HarrySkySon/BitForge-SDR/schematics/All_Bloks_of_project.kicad_sch

## KiCad design schematics/All_Bloks_of_project.kicad_sch (2026-03-29)

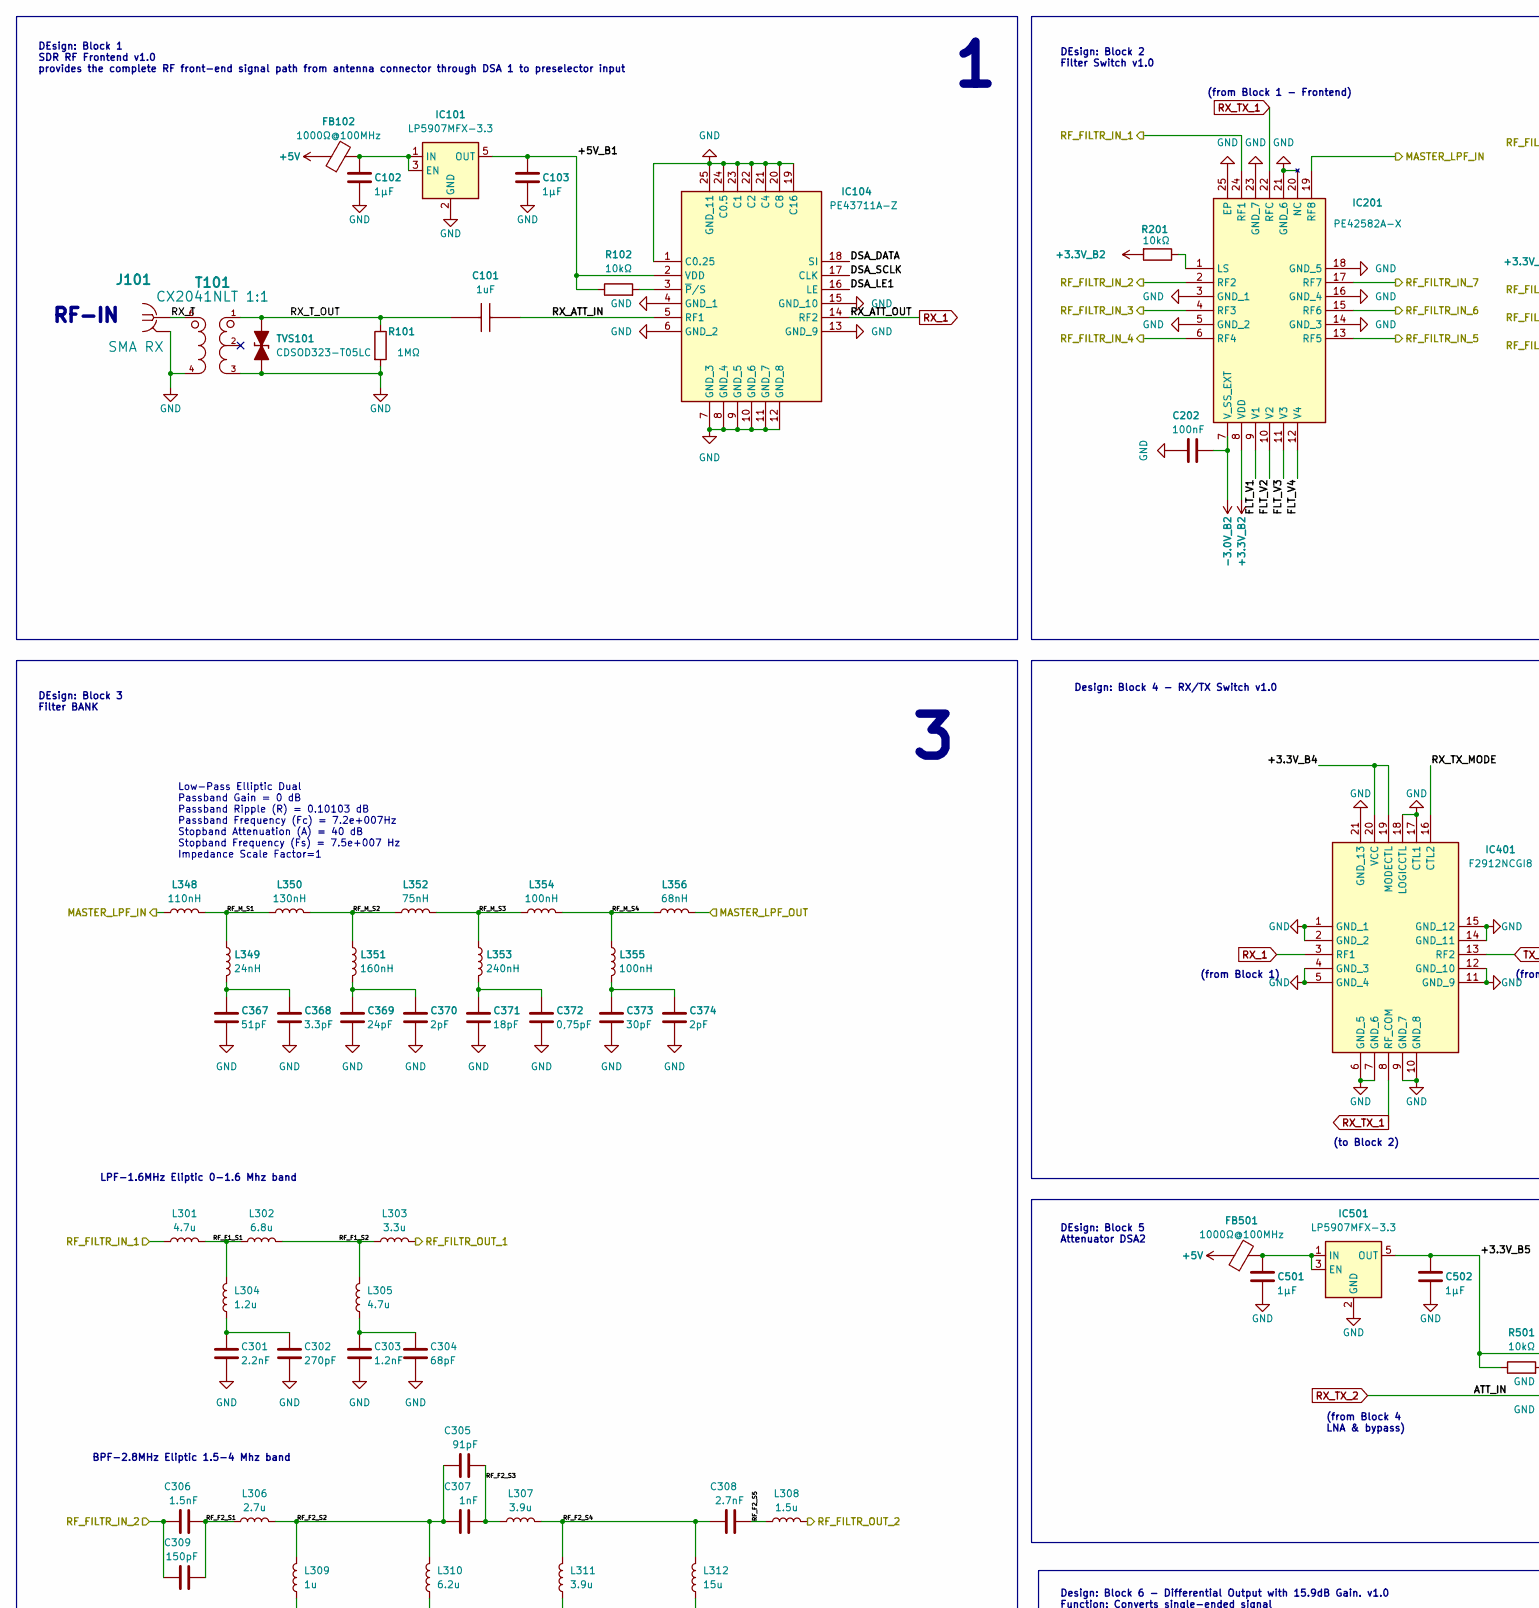
[picture p2: schematic All_Bloks_of_project.kicad_sch, part in row 1, column 1]

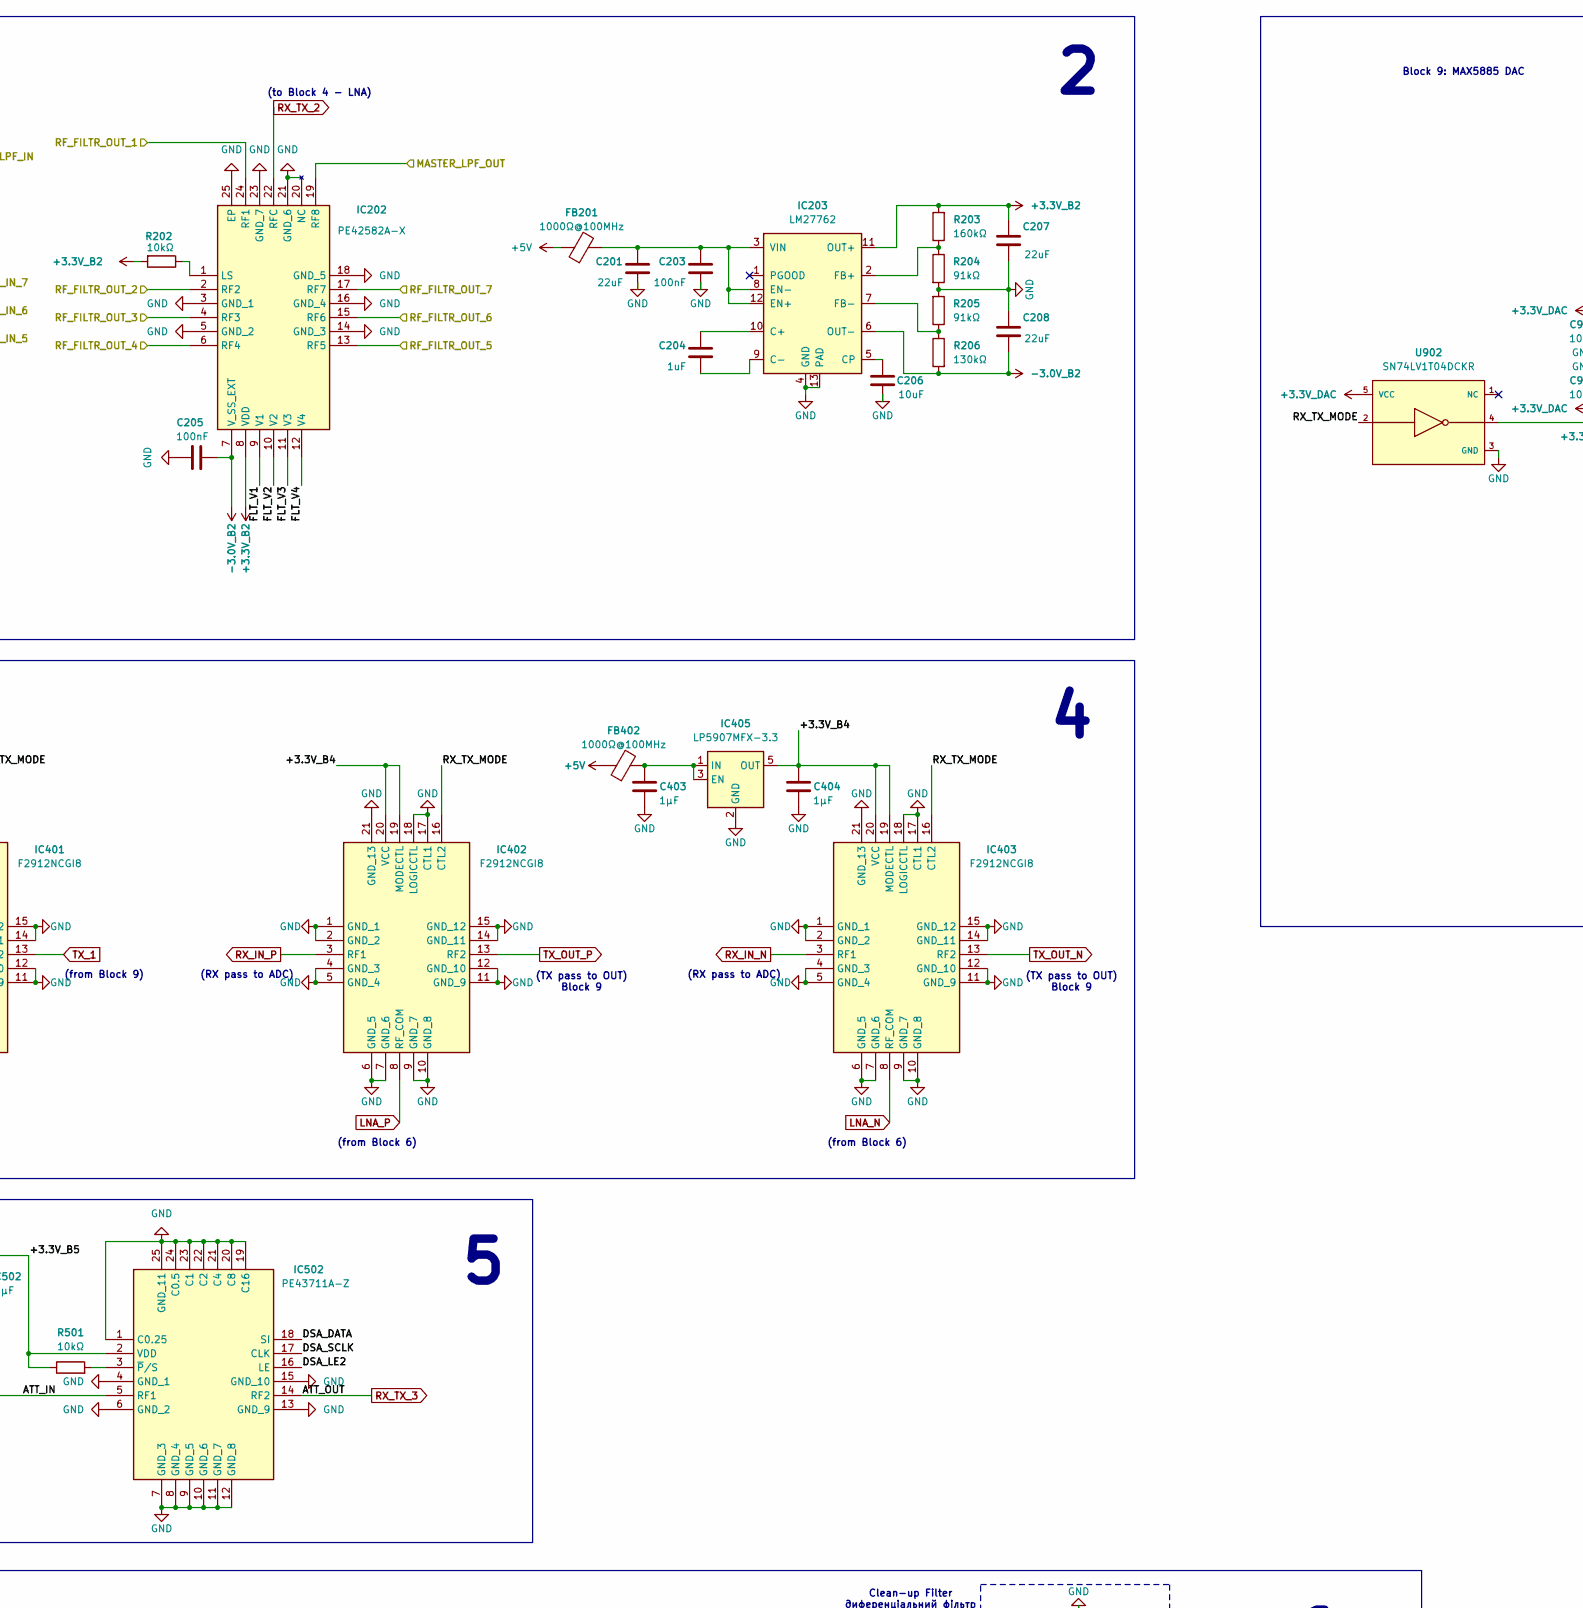
[picture p3: schematic All_Bloks_of_project.kicad_sch, part in row 1, column 2]

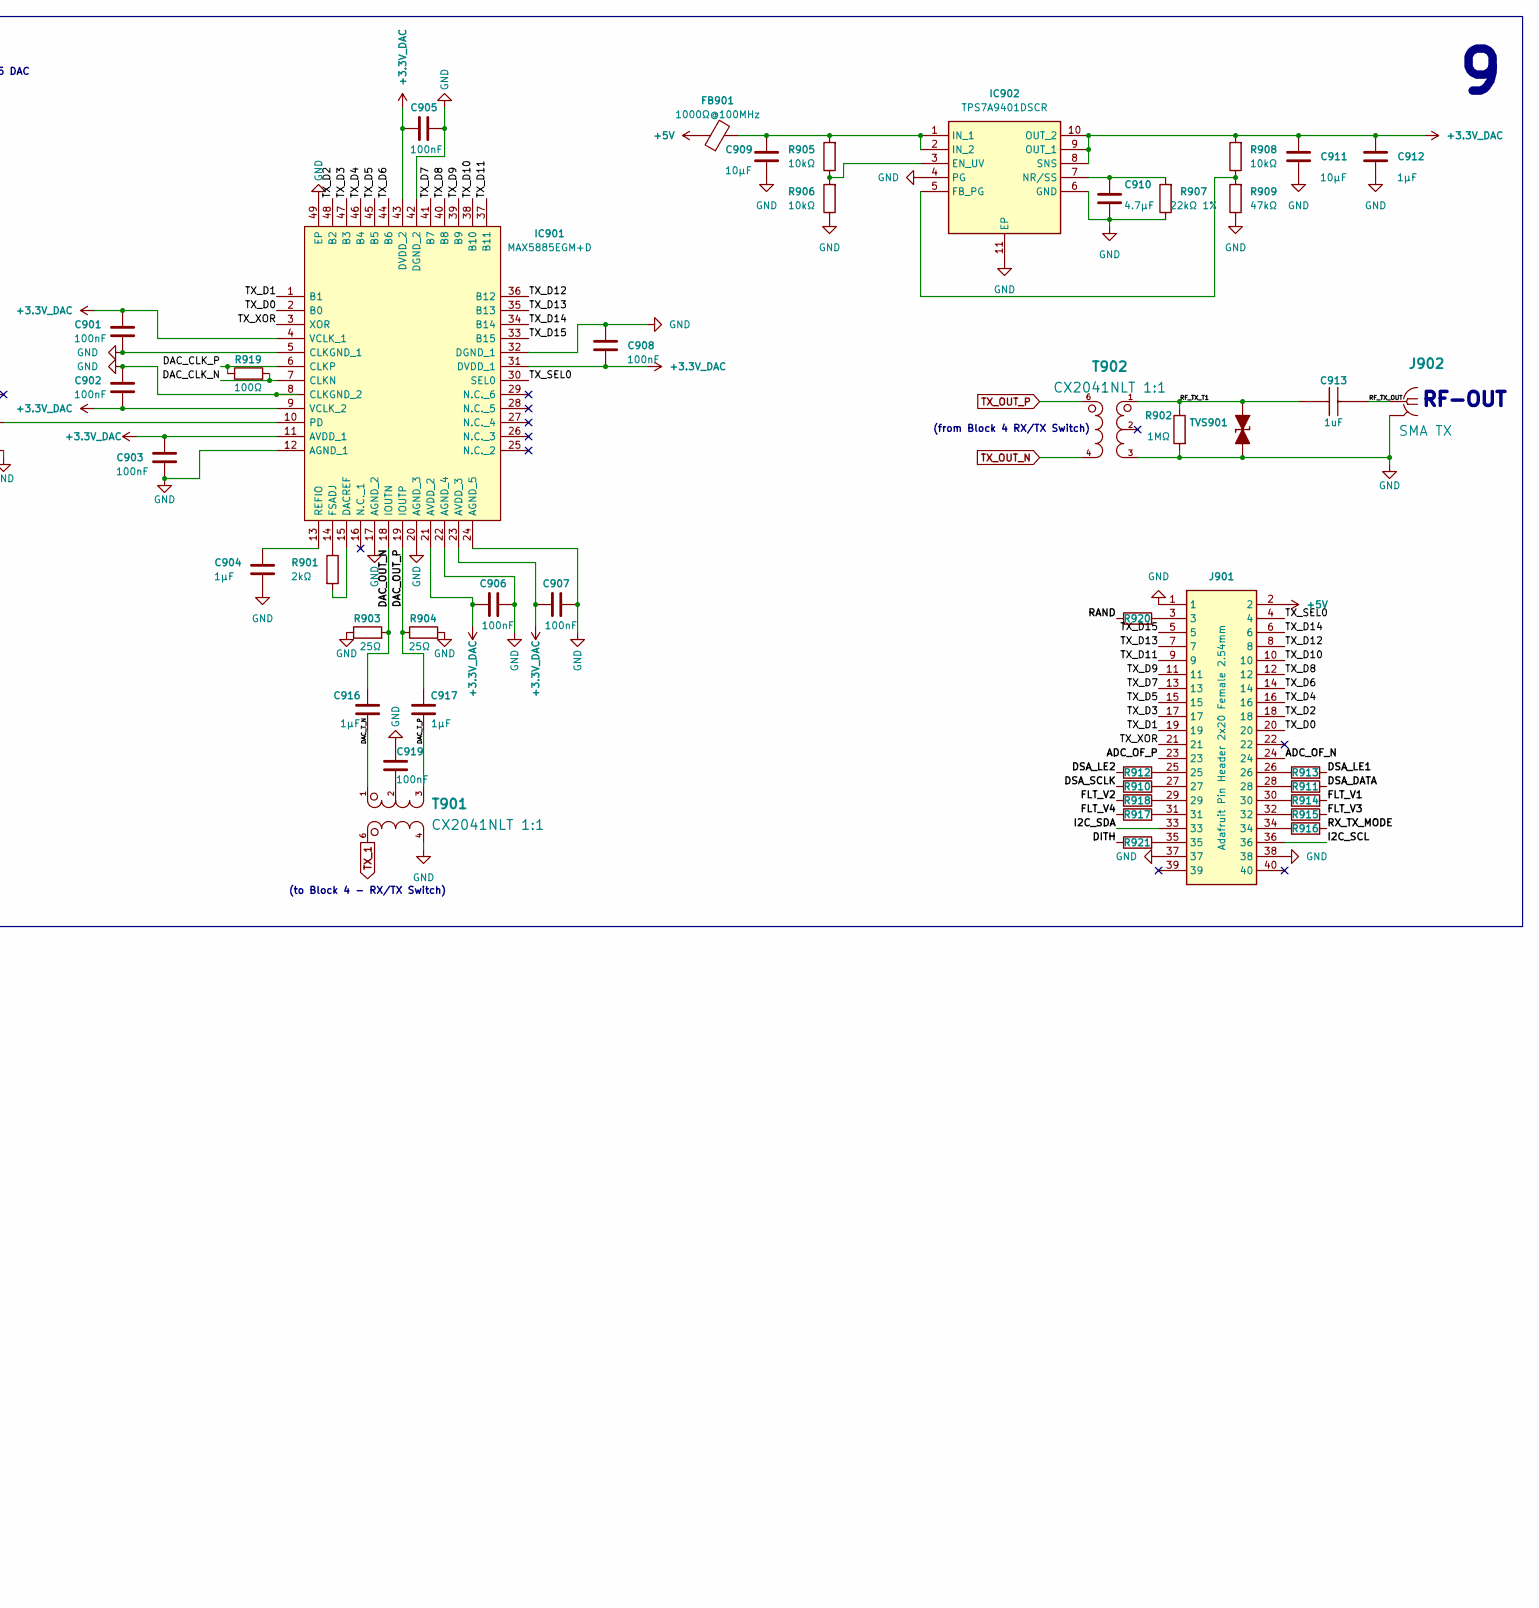
[picture p4: schematic All_Bloks_of_project.kicad_sch, part in row 1, column 3]

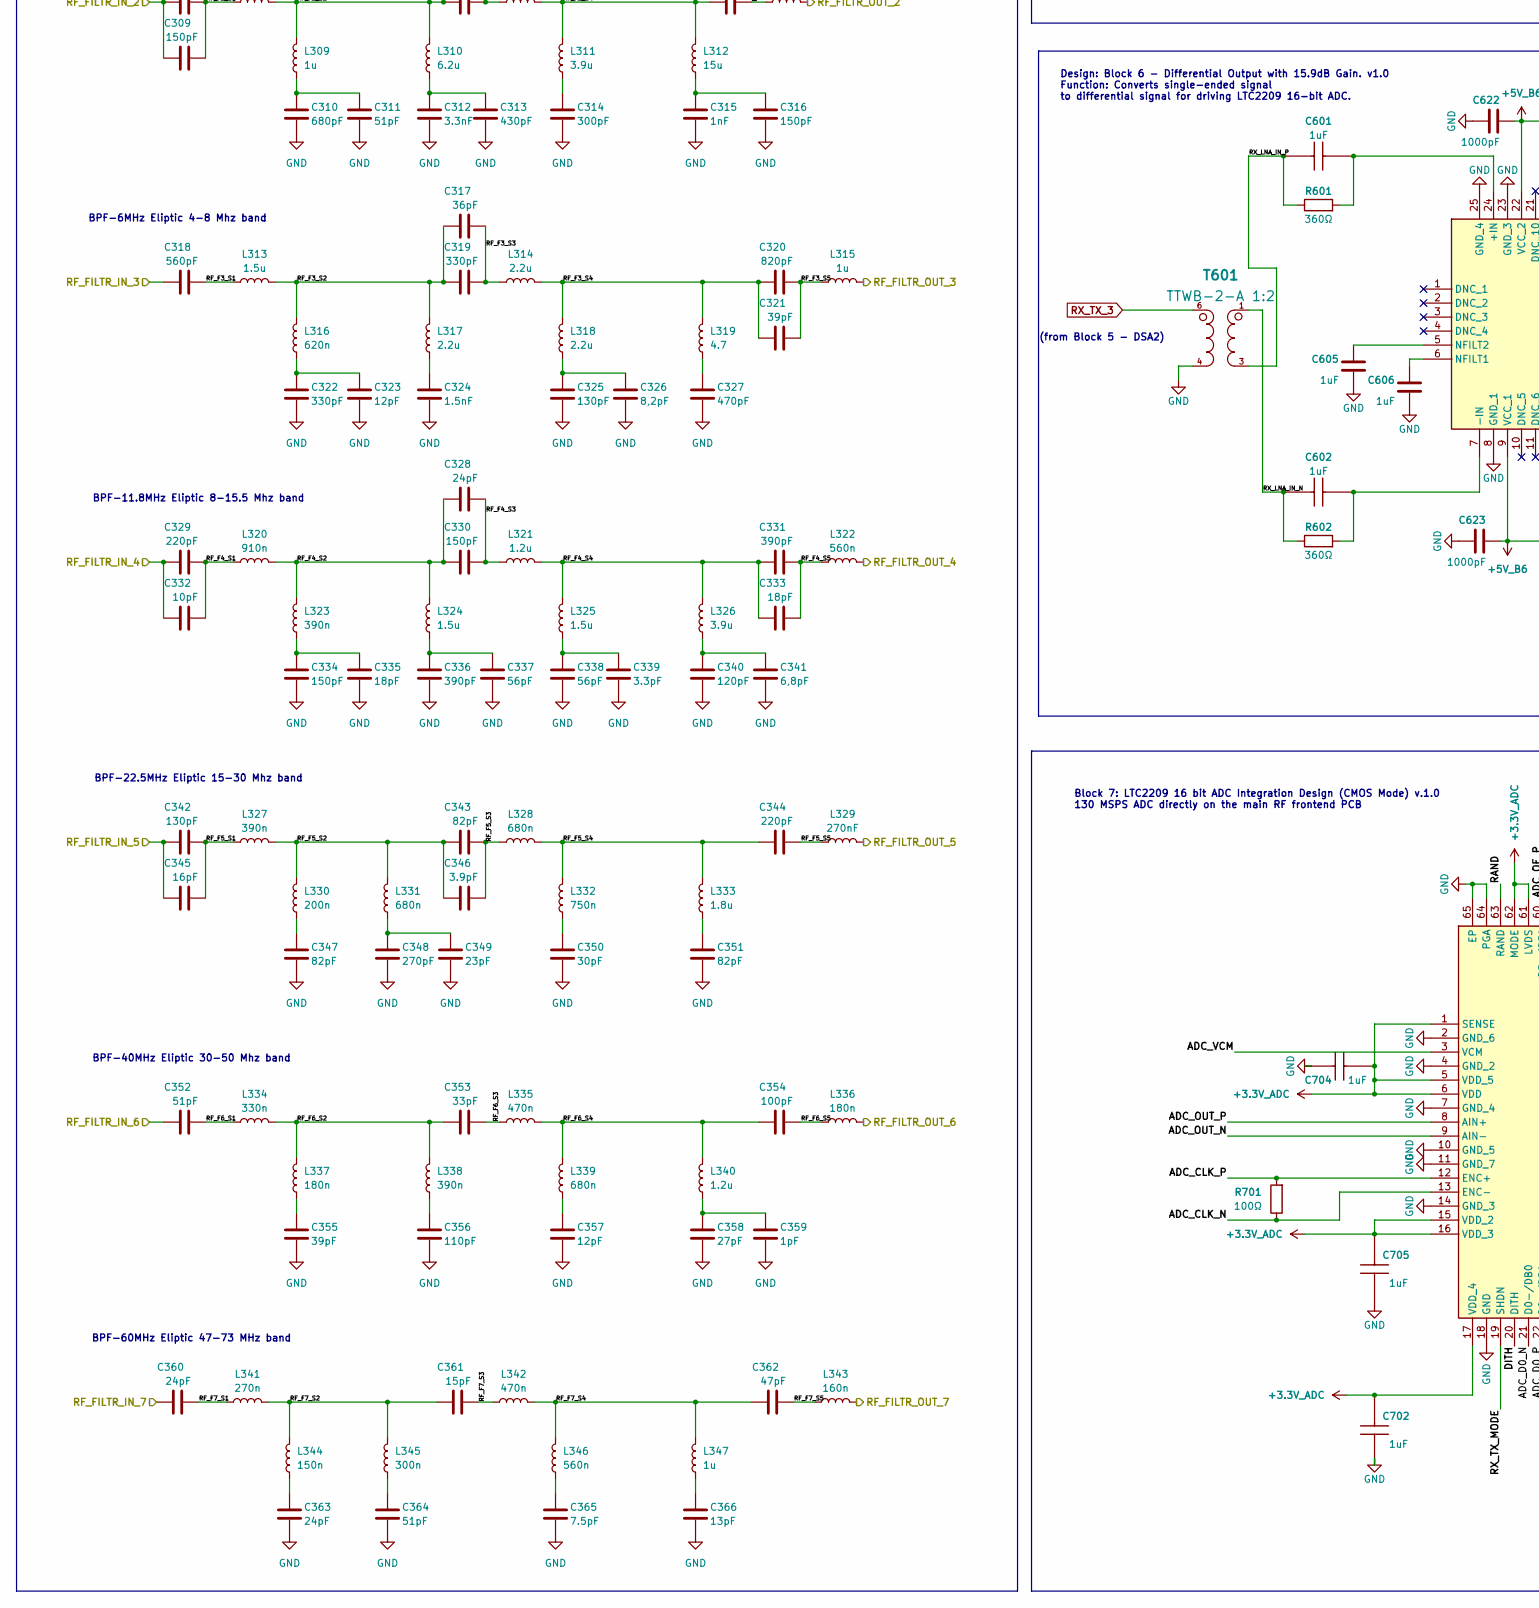
[picture p5: schematic All_Bloks_of_project.kicad_sch, part in row 2, column 1]

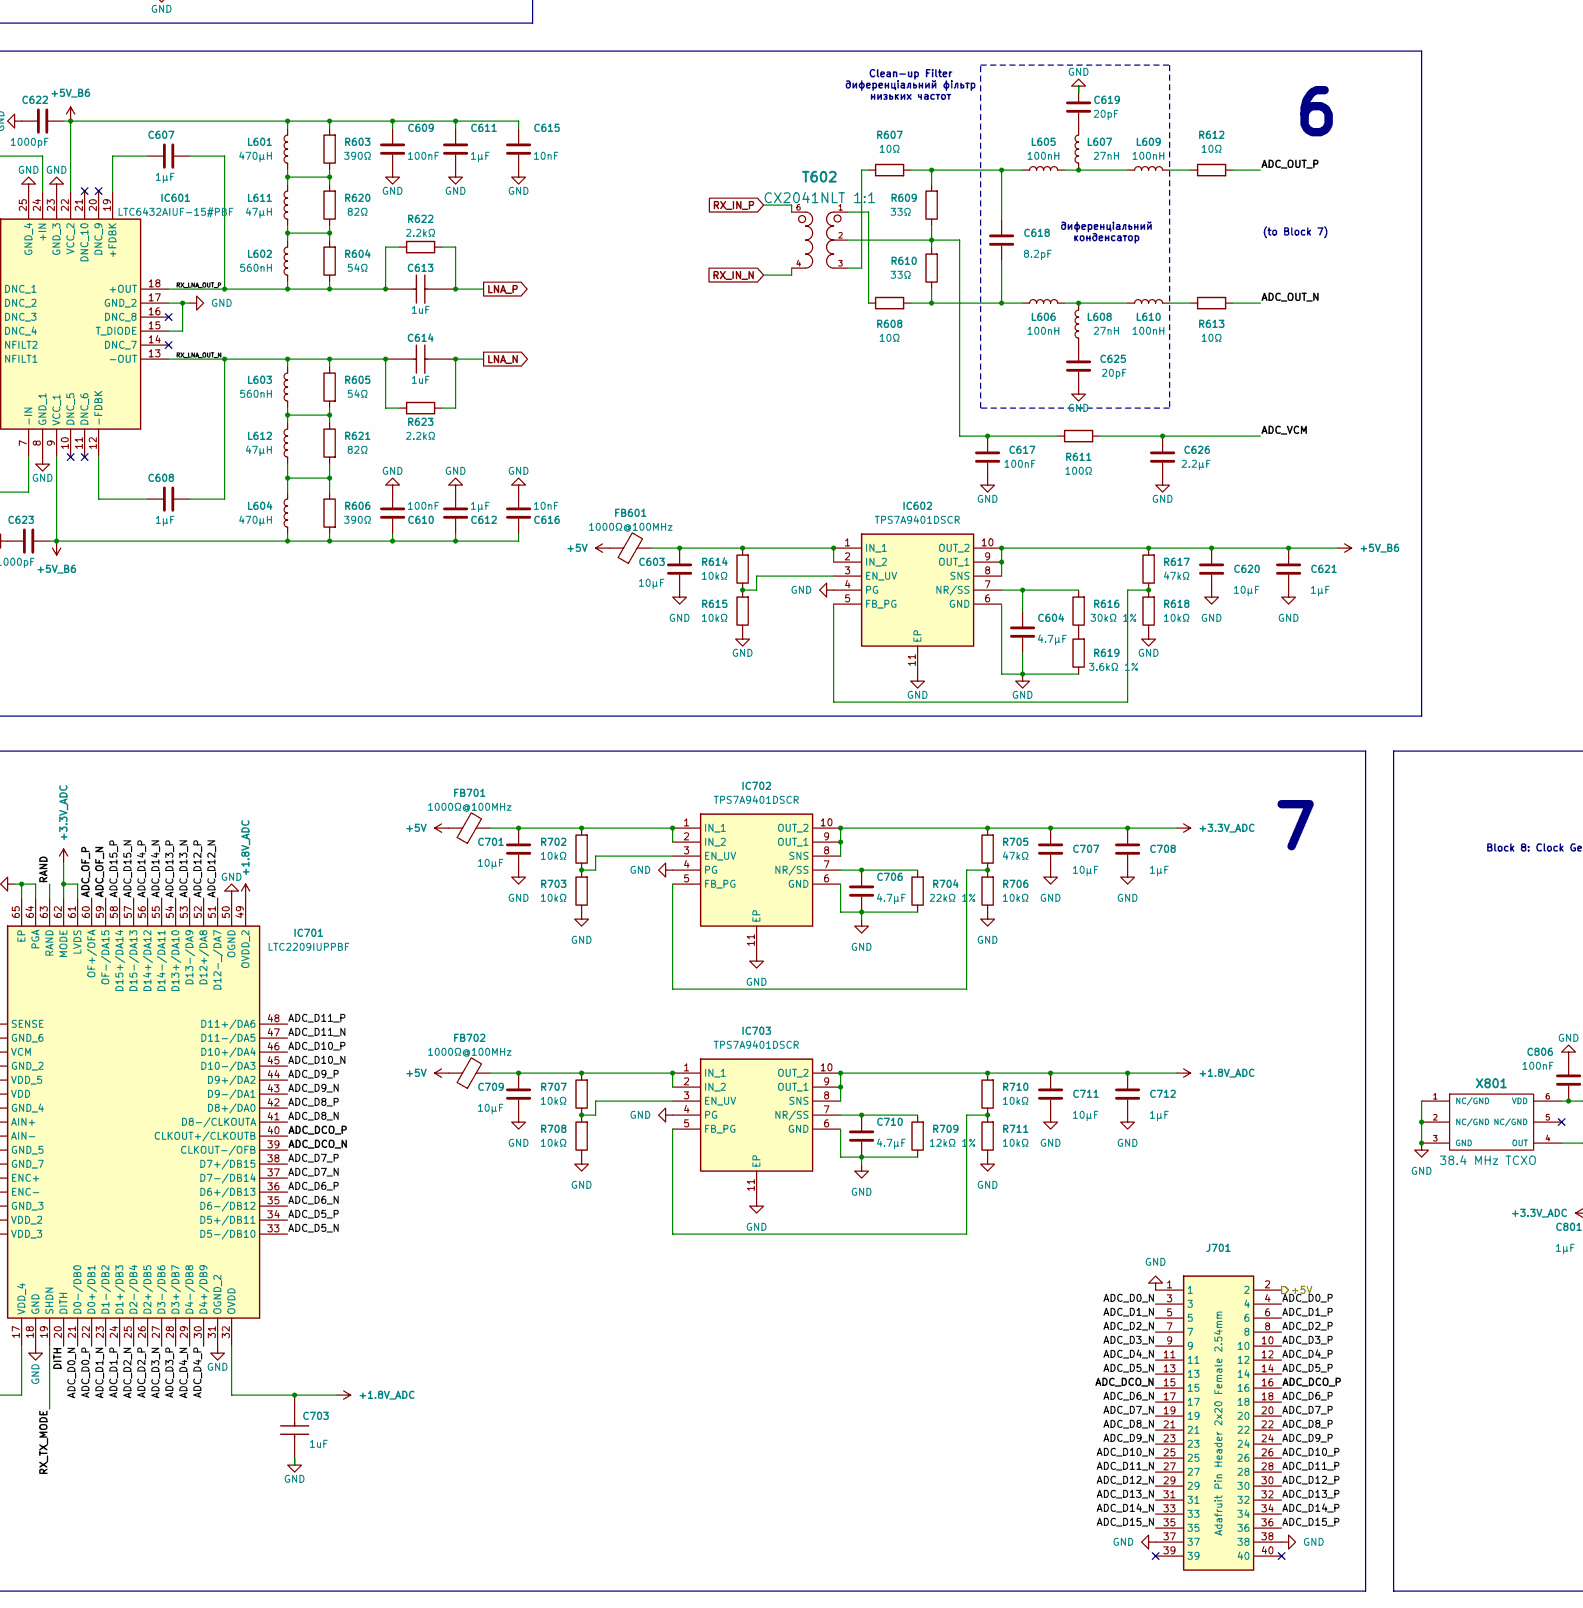
[picture p6: schematic All_Bloks_of_project.kicad_sch, part in row 2, column 2]

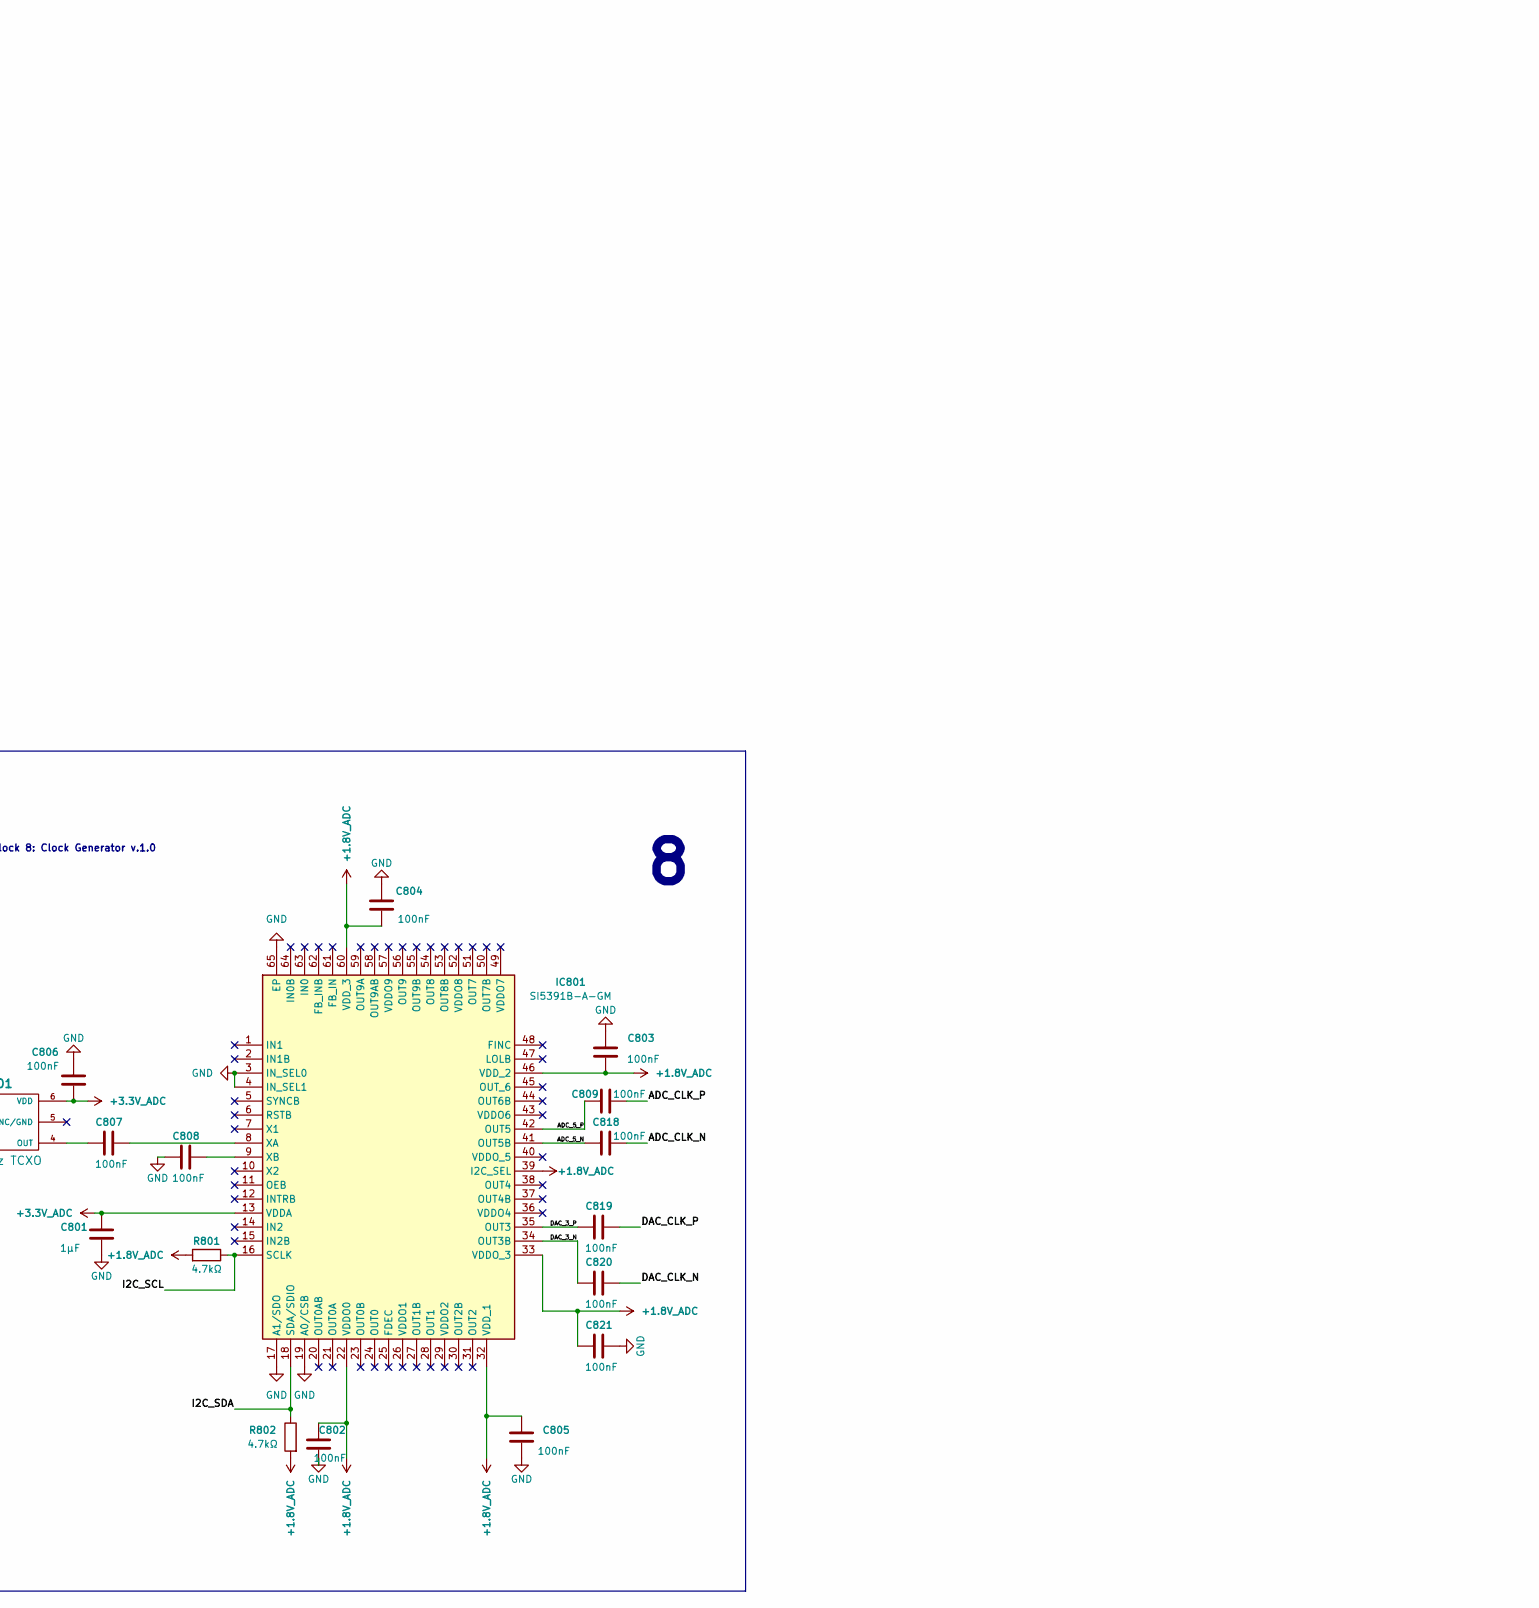
[picture p7: schematic All_Bloks_of_project.kicad_sch, part in row 2, column 3]

Parts:
C101, C601, C602, C613, C614, C702, C703, C704, C705, C913: 1uF; 0508; Manufacturer_Part_Number 0508ZC105KAT2A; Mouser Part Number 581-0508ZC105K
C102, C103, C403, C404, C501, C502, C607, C608, C621, C708, C712, C801, C904, C912: 1µF; C_0603_1608Metric
C201, C207, C208: 22uF; C_0603_1608Metric
C202, C203, C205, C617, C802, C803, C804, C805, C806, C807, C808, C809, C818, C819, C820, C821, C901, C902, C903, C905, C906, C907, C908, C919: 100nF; C_0603_1608Metric
C204, C605, C606: 1uF; C_0603_1608Metric
C206: 10uF; C_0603_1608Metric
C301: 2.2nF; C_0603_1608Metric
C302, C348: 270pF; C_0603_1608Metric
C303: 1.2nF; C_0603_1608Metric
C304: 68pF; C_0603_1608Metric
C305: 91pF; C_0603_1608Metric
C306, C324: 1.5nF; C_0603_1608Metric
C307, C315: 1nF; C_0603_1608Metric
C308: 2.7nF; C_0603_1608Metric
C309, C316, C330, C334: 150pF; C_0603_1608Metric
C310: 680pF; C_0603_1608Metric
C311, C352, C364, C367: 51pF; C_0603_1608Metric
C312: 3.3nF; C_0603_1608Metric
C313: 430pF; C_0603_1608Metric
C314: 300pF; C_0603_1608Metric
C317: 36pF; C_0603_1608Metric
C318: 560pF; C_0603_1608Metric
C319, C322: 330pF; C_0603_1608Metric
C320: 820pF; C_0603_1608Metric
C321, C355: 39pF; C_0603_1608Metric
C323, C357: 12pF; C_0603_1608Metric
C325, C342: 130pF; C_0603_1608Metric
C326: 8,2pF; C_0603_1608Metric
C327: 470pF; C_0603_1608Metric
C328, C360, C363, C369: 24pF; C_0603_1608Metric
C329, C344: 220pF; C_0603_1608Metric
C331, C336: 390pF; C_0603_1608Metric
C332: 10pF; C_0603_1608Metric
C333, C335, C371: 18pF; C_0603_1608Metric
C337, C338: 56pF; C_0603_1608Metric
C339, C368: 3.3pF; C_0603_1608Metric
C340: 120pF; C_0603_1608Metric
C341: 6,8pF; C_0603_1608Metric
C343, C347, C351: 82pF; C_0603_1608Metric
C345: 16pF; C_0603_1608Metric
C346: 3.9pF; C_0603_1608Metric
C349: 23pF; C_0603_1608Metric
C350, C373: 30pF; C_0603_1608Metric
C353: 33pF; C_0603_1608Metric
C354: 100pF; C_0603_1608Metric
C356: 110pF; C_0603_1608Metric
C358: 27pF; C_0603_1608Metric
C359: 1pF; C_0603_1608Metric
C361: 15pF; C_0603_1608Metric
C362: 47pF; C_0603_1608Metric
C365: 7.5pF; C_0603_1608Metric
C366: 13pF; C_0603_1608Metric
C370, C374: 2pF; C_0603_1608Metric
C372: 0,75pF; C_0603_1608Metric
C603, C620, C701, C707, C709, C711, C909, C911: 10µF; C_0603_1608Metric
C604, C706, C710, C910: 4.7µF; C_0603_1608Metric
C609, C610: 100nF; L_0805_2012Metric
C611, C612: 1µF; L_0805_2012Metric
C615, C616: 10nF; L_0805_2012Metric
C618: 8.2pF; C_0603_1608Metric
C619, C625: 20pF; C_0603_1608Metric
C622, C623: 1000pF; C_0603_1608Metric
C626: 2.2µF; C_0603_1608Metric
C916, C917: 1µF; C_0805_2012Metric
FB102, FB201, FB402, FB501, FB601, FB701, FB702, FB901: 1000Ω@100MHz; L_0603_1608Metric
IC101, IC405, IC501: LP5907MFX-3.3; SOT-23-5
IC104, IC502: PE43711A-Z; QFN50P400X400X90-25N-D; Manufacturer_Part_Number PE43711A-Z
IC201, IC202: PE42582A-X; QFN50P400X400X90-25N-D; Manufacturer_Part_Number PE42582A-X; Mouser Part Number 81-PE42582A-X
IC203: LM27762; WSON-12-1EP_3x2mm_P0.5mm_EP1x2.65_ThermalVias
IC401, IC402, IC403: F2912NCGI8; QFN50P400X400X80-21N-D; Mouser Part Number 972-F2912NCGI8
IC601: LTC6432AIUF-15#PBF; QFN50P400X400X80-25N-D; Mouser Part Number 584-6432AIUF15PBF
IC602, IC702, IC703, IC902: TPS7A9401DSCR; SON50P300X300X80-11N-D; Manufacturer_Part_Number TPS7A9401DSCR; Mouser Part Number 595-TPS7A9401DSCR
IC701: LTC2209IUPPBF; QFN50P900X900X80-65N; Manufacturer_Part_Number LTC2209IUPPBF
IC801: SI5391B-A-GM; QFN50P900X900X90-65N-D; Manufacturer_Part_Number SI5391B-A-GM; Mouser Part Number 634-SI5391B-A-GM
IC901: MAX5885EGM+D; QFN50P700X700X100-49N; Manufacturer_Part_Number MAX5885EGM+D; Mouser Part Number 700-MAX5885EGMD
J101: SMA RX; SMA_BAT_Wireless_BWSMA-KWE-Z001
J701, J901: Adafruit Pin Header 2x20 Female 2.54mm; PinHeader_2x20_P2.54mm_Vertical; Manufacturer_Part_Number 2222; Mouser Part Number 485-2222
J902: SMA TX; SMA_BAT_Wireless_BWSMA-KWE-Z001
L301, L305: 4.7u; L_1008_2520Metric
L302: 6.8u; L_1210_3225Metric
L303: 3.3u; L_1008_2520Metric
L304, L321, L340: 1.2u; L_1008_2520Metric
L306: 2.7u; L_1008_2520Metric
L307, L311, L326: 3.9u; L_1008_2520Metric
L308, L313, L324, L325: 1.5u; L_1008_2520Metric
L309, L315, L347: 1u; L_1008_2520Metric
L310: 6.2u; L_1008_2520Metric
L312: 15u; L_1008_2520Metric
L314, L317, L318: 2.2u; L_1008_2520Metric
L316: 620n; L_1008_2520Metric
L319: 4.7; L_1008_2520Metric
L320: 910n; L_1008_2520Metric
L322, L346: 560n; L_1008_2520Metric
L323, L327, L338: 390n; L_1008_2520Metric
L328, L331, L339: 680n; L_1008_2520Metric
L329: 270nF; L_1008_2520Metric
L330: 200n; L_0603_1608Metric
L332: 750n; L_1008_2520Metric
L333: 1.8u; L_1008_2520Metric
L334: 330n; L_1008_2520Metric
L335, L342: 470n; L_1008_2520Metric
L336, L337: 180n; L_0603_1608Metric
L341: 270n; L_1008_2520Metric
L343: 160n; L_0603_1608Metric
L344: 150n; L_1008_2520Metric
L345: 300n; L_0603_1608Metric
L348: 110nH; L_0603_1608Metric
L349: 24nH; L_0603_1608Metric
L350: 130nH; L_0603_1608Metric
L351: 160nH; L_0603_1608Metric
L352: 75nH; L_0603_1608Metric
L353: 240nH; L_0805_2012Metric
L354, L355, L605, L606, L609, L610: 100nH; L_0603_1608Metric
L356: 68nH; L_0603_1608Metric
L601, L604: 470µH; L_Changjiang_FNR8065S
L602, L603: 560nH; L_Sunlord_SWPA252010S
L607, L608: 27nH; L_0603_1608Metric
L611, L612: 47µH; L_Sunlord_SWPA4030S
R101, R902: 1MΩ; R_0603_1608Metric
R102, R201, R202, R501, R614, R615, R618, R702, R703, R706, R707, R708, R710, R711, R905, R906, R908: 10kΩ; R_0603_1608Metric
R203: 160kΩ; R_0603_1608Metric
R204, R205: 91kΩ; R_0603_1608Metric
R206: 130kΩ; R_0603_1608Metric
R601, R602: 360Ω; R_0603_1608Metric
R603, R606: 390Ω; R_0603_1608Metric
R604, R605: 54Ω; R_0603_1608Metric
R607, R608, R612, R613: 10Ω; R_0603_1608Metric
R609, R610: 33Ω; R_0603_1608Metric
R611, R701, R919: 100Ω; R_0603_1608Metric
R616: 30kΩ 1%; R_0603_1608Metric
R617, R705, R909: 47kΩ; R_0603_1608Metric
R619: 3.6kΩ 1%; R_0603_1608Metric
R620, R621: 82Ω; R_0603_1608Metric
R622, R623: 2.2kΩ; R_0603_1608Metric
R704, R907: 22kΩ 1%; R_0603_1608Metric
R709: 12kΩ 1%; R_0603_1608Metric
R801, R802: 4.7kΩ; R_0603_1608Metric
R901: 2kΩ; R_0603_1608Metric
R903, R904: 25Ω; R_0603_1608Metric
R910, R911, R912, R913, R914, R915, R916, R917, R918, R920, R921: 47Ω; R_0603_1608Metric
T101, T602, T901, T902: CX2041NLT 1:1; CX2041NLT
T601: TTWB-2-A 1:2; TTWB20101LB
TVS101, TVS901: CDSOD323-T05LC; D_SOD-323_HandSoldering
U902: SN74LV1T04DCKR; Texas_Instruments-DCK0005A-0-0-IPC_C; mouser part number 595-SN74LV1T04DCKR; digikey description IC INVERTER 1CH 1-INP SC70-5
X801: 38.4 MHz TCXO; Oscillator_SMD_Kyocera_2520-6Pin_2.5x2.0mm

Connections:
+1.8V_ADC: C703.2, C711.1, C712.1, C802.1, C803.2, C804.2, C805.1, C821.1, IC701.32 (OVDD), IC701.49 (OVDD_2), IC703.8 (SNS), IC703.9 (OUT_1), IC703.10 (OUT_2), IC801.22 (VDDO0), IC801.32 (VDD_1), IC801.33 (VDDO_3), IC801.39 (I2C_SEL), IC801.46 (VDD_2), IC801.60 (VDD_3), R710.2, R801.2, R802.2
+3.3V_ADC: C702.2, C704.2, C705.2, C707.1, C708.1, C801.1, C806.2, IC701.1 (SENSE), IC701.5 (VDD_5), IC701.6 (VDD), IC701.15 (VDD_2), IC701.16 (VDD_3), IC701.17 (VDD_4), IC701.61 (LVDS), IC701.62 (MODE), IC702.8 (SNS), IC702.9 (OUT_1), IC702.10 (OUT_2), IC801.13 (VDDA), R705.2, X801.6 (VDD)
+3.3V_B2: C207.2, IC201.8 (VDD), IC202.8 (VDD), IC203.11 (OUT+), R201.2, R202.2, R203.2
+3.3V_B4: C404.1, IC401.19 (MODECTL), IC401.20 (VCC), IC402.19 (MODECTL), IC402.20 (VCC), IC403.19 (MODECTL), IC403.20 (VCC), IC405.5 (OUT)
+3.3V_B5: C502.1, IC501.5 (OUT), IC502.2 (VDD), R501.1
+3.3V_DAC: C901.1, C902.1, C903.1, C905.2, C906.1, C907.1, C908.2, C911.1, C912.1, IC901.4 (VCLK_1), IC901.9 (VCLK_2), IC901.11 (AVDD_1), IC901.21 (AVDD_2), IC901.23 (AVDD_3), IC901.31 (DVDD_1), IC901.43 (DVDD_2), IC902.8 (SNS), IC902.9 (OUT_1), IC902.10 (OUT_2), R908.2, U902.5 (VCC)
+5V: FB102.1, FB201.1, FB402.1, FB501.1, FB601.1, FB701.1, FB702.1, FB901.1, J701.2, J901.2
+5V_B1: C103.1, IC101.5 (OUT), IC104.2 (VDD), R102.1
+5V_B6: C609.1, C610.1, C611.1, C612.1, C615.1, C616.1, C620.1, C621.1, C622.2, C623.2, IC601.9 (VCC_1), IC601.22 (VCC_2), IC602.8 (SNS), IC602.9 (OUT_1), IC602.10 (OUT_2), L601.1, L604.2, R603.2, R606.2, R617.2
-3.0V_B2: C202.1, C205.1, C208.2, IC201.7 (V_SS_EXT), IC202.7 (V_SS_EXT), IC203.6 (OUT-), R206.2
ADC_5_N: C818.1, IC801.41 (OUT5B)
ADC_5_P: C809.1, IC801.42 (OUT5)
ADC_CLK_N: C818.2, IC701.13 (ENC-), R701.1
ADC_CLK_P: C809.2, IC701.12 (ENC+), R701.2
ADC_D0_N: IC701.21 (D0-/DB0), J701.3
ADC_D0_P: IC701.22 (D0+/DB1), J701.4
ADC_D1_N: IC701.23 (D1-/DB2), J701.5
ADC_D1_P: IC701.24 (D1+/DB3), J701.6
ADC_D2_N: IC701.25 (D2-/DB4), J701.7
ADC_D2_P: IC701.26 (D2+/DB5), J701.8
ADC_D3_N: IC701.27 (D3-/DB6), J701.9
ADC_D3_P: IC701.28 (D3+/DB7), J701.10
ADC_D4_N: IC701.29 (D4-/DB8), J701.11
ADC_D4_P: IC701.30 (D4+/DB9), J701.12
ADC_D5_N: IC701.33 (D5-/DB10), J701.13
ADC_D5_P: IC701.34 (D5+/DB11), J701.14
ADC_D6_N: IC701.35 (D6-/DB12), J701.17
ADC_D6_P: IC701.36 (D6+/DB13), J701.18
ADC_D7_N: IC701.37 (D7-/DB14), J701.19
ADC_D7_P: IC701.38 (D7+/DB15), J701.20
ADC_D8_N: IC701.41 (D8-/CLKOUTA), J701.21
ADC_D8_P: IC701.42 (D8+/DA0), J701.22
ADC_D9_N: IC701.43 (D9-/DA1), J701.23
ADC_D9_P: IC701.44 (D9+/DA2), J701.24
ADC_D10_N: IC701.45 (D10-/DA3), J701.25
ADC_D10_P: IC701.46 (D10+/DA4), J701.26
ADC_D11_N: IC701.47 (D11-/DA5), J701.27
ADC_D11_P: IC701.48 (D11+/DA6), J701.28
ADC_D12_N: IC701.51 (D12-_/DA7), J701.29
ADC_D12_P: IC701.52 (D12+/DA8), J701.30
ADC_D13_N: IC701.53 (D13-/DA9), J701.31
ADC_D13_P: IC701.54 (D13+/DA10), J701.32
ADC_D14_N: IC701.55 (D14-/DA11), J701.33
ADC_D14_P: IC701.56 (D14+/DA12), J701.34
ADC_D15_N: IC701.57 (D15-/DA13), J701.35
ADC_D15_P: IC701.58 (D15+/DA14), J701.36
ADC_DCO_N: IC701.39 (CLKOUT-/OFB), J701.15
ADC_DCO_P: IC701.40 (CLKOUT+/CLKOUTB), J701.16
ADC_OF_N: IC701.59 (OF-/DA15), J901.24
ADC_OF_P: IC701.60 (OF+/OFA), J901.23
ADC_OUT_N: IC701.9 (AIN-), R613.2
ADC_OUT_P: IC701.8 (AIN+), R612.2
ADC_VCM: C626.2, IC701.3 (VCM), R611.2
DAC_3_N: C820.1, IC801.34 (OUT3B)
DAC_3_P: C819.1, IC801.35 (OUT3)
DAC_CLK_N: C820.2, IC901.7 (CLKN), R919.2
DAC_CLK_P: C819.2, IC901.6 (CLKP), R919.1
DAC_OUT_N: C916.1, IC901.18 (IOUTN), R903.2
DAC_OUT_P: C917.1, IC901.19 (IOUTP), R904.1
DAC_T_N: C916.2, T901.1 (S1)
DAC_T_P: C917.2, T901.3 (S2)
DITH: IC701.20 (DITH), R921.1
DSA_DATA: IC104.18 (SI), IC502.18 (SI), R911.2
DSA_LE1: IC104.16 (LE), R913.2
DSA_LE2: IC502.16 (LE), R912.1
DSA_SCLK: IC104.17 (CLK), IC502.17 (CLK), R910.1
FLT_V1: IC201.9 (V1), IC202.9 (V1), R914.2
FLT_V2: IC201.10 (V2), IC202.10 (V2), R918.1
FLT_V3: IC201.11 (V3), IC202.11 (V3), R915.2
FLT_V4: IC201.12 (V4), IC202.12 (V4), R917.1
GND: C102.2, C103.2, C201.1, C202.2, C203.1, C205.2, C206.1, C207.1, C208.1, C301.2, C302.2, C303.2, C304.2, C310.2, C311.2, C312.2, C313.2, C314.2, C315.2, C316.2, C322.2, C323.2, C324.2, C325.2, C326.2, C327.2, C334.2, C335.2, C336.2, C337.2, C338.2, C339.2, C340.2, C341.2, C347.2, C348.2, C349.2, C350.2, C351.2, C355.2, C356.2, C357.2, C358.2, C359.2, C363.2, C364.2, C365.2, C366.2, C367.2, C368.2, C369.2, C370.2, C371.2, C372.2, C373.2, C374.2, C403.2, C404.2, C501.2, C502.2, C603.2, C604.2, C605.1, C606.1, C609.2, C610.2, C611.2, C612.2, C615.2, C616.2, C617.1, C619.1, C620.2, C621.2, C622.1, C623.1, C625.1, C626.1, C701.2, C702.1, C703.1, C704.1, C705.1, C706.2, C707.2, C708.2, C709.2, C710.2, C711.2, C712.2, C801.2, C802.2, C803.1, C804.1, C805.2, C806.1, C808.1, C821.2, C901.2, C902.2, C903.2, C904.2, C905.1, C906.2, C907.2, C908.1, C909.2, C910.2, C911.2, C912.2, C919.2, IC101.2 (GND), IC104.1 (C0.25), IC104.4 (GND_1), IC104.6 (GND_2), IC104.7 (GND_3), IC104.8 (GND_4), IC104.9 (GND_5), IC104.10 (GND_6), IC104.11 (GND_7), IC104.12 (GND_8), IC104.13 (GND_9), IC104.15 (GND_10), IC104.19 (C16), IC104.20 (C8), IC104.21 (C4), IC104.22 (C2), IC104.23 (C1), IC104.24 (C0.5), IC104.25 (GND_11), IC201.3 (GND_1), IC201.5 (GND_2), IC201.14 (GND_3), IC201.16 (GND_4), IC201.18 (GND_5), IC201.20 (NC), IC201.21 (GND_6), IC201.23 (GND_7), IC201.25 (EP), IC202.3 (GND_1), IC202.5 (GND_2), IC202.14 (GND_3), IC202.16 (GND_4), IC202.18 (GND_5), IC202.20 (NC), IC202.21 (GND_6), IC202.23 (GND_7), IC202.25 (EP), IC203.4 (GND), IC203.13 (PAD), IC401.1 (GND_1), IC401.2 (GND_2), IC401.4 (GND_3), IC401.5 (GND_4), IC401.6 (GND_5), IC401.7 (GND_6), IC401.9 (GND_7), IC401.10 (GND_8), IC401.11 (GND_9), IC401.12 (GND_10), IC401.14 (GND_11), IC401.15 (GND_12), IC401.17 (CTL1), IC401.18 (LOGICCTL), IC401.21 (GND_13), IC402.1 (GND_1), IC402.2 (GND_2), IC402.4 (GND_3), IC402.5 (GND_4), IC402.6 (GND_5), IC402.7 (GND_6), IC402.9 (GND_7), IC402.10 (GND_8), IC402.11 (GND_9), IC402.12 (GND_10), IC402.14 (GND_11), IC402.15 (GND_12), IC402.17 (CTL1), IC402.18 (LOGICCTL), IC402.21 (GND_13), IC403.1 (GND_1), IC403.2 (GND_2), IC403.4 (GND_3), IC403.5 (GND_4), IC403.6 (GND_5), IC403.7 (GND_6), IC403.9 (GND_7), IC403.10 (GND_8), IC403.11 (GND_9), IC403.12 (GND_10), IC403.14 (GND_11), IC403.15 (GND_12), IC403.17 (CTL1), IC403.18 (LOGICCTL), IC403.21 (GND_13), IC405.2 (GND), IC501.2 (GND), IC502.1 (C0.25), IC502.4 (GND_1), IC502.6 (GND_2), IC502.7 (GND_3), IC502.8 (GND_4), IC502.9 (GND_5), IC502.10 (GND_6), IC502.11 (GND_7), IC502.12 (GND_8), IC502.13 (GND_9), IC502.15 (GND_10), IC502.19 (C16), IC502.20 (C8), IC502.21 (C4), IC502.22 (C2), IC502.23 (C1), IC502.24 (C0.5), IC502.25 (GND_11), IC601.8 (GND_1), IC601.15 (T_DIODE), IC601.17 (GND_2), IC601.23 (GND_3), IC601.25 (GND_4), IC602.4 (PG), IC602.6 (GND), IC602.11 (EP), IC701.2 (GND_6), IC701.4 (GND_2), IC701.7 (GND_4), IC701.10 (GND_5), IC701.11 (GND_7), IC701.14 (GND_3), IC701.18 (GND), IC701.31 (OGND_2), IC701.50 (OGND), IC701.64 (PGA), IC701.65 (EP), IC702.4 (PG), IC702.6 (GND), IC702.11 (EP), IC703.4 (PG), IC703.6 (GND), IC703.11 (EP), IC801.3 (IN_SEL0), IC801.4 (IN_SEL1), IC801.17 (A1/SDO), IC801.19 (A0/CSB), IC801.65 (EP), IC901.5 (CLKGND_1), IC901.8 (CLKGND_2), IC901.12 (AGND_1), IC901.17 (AGND_2), IC901.20 (AGND_3), IC901.22 (AGND_4), IC901.24 (AGND_5), IC901.32 (DGND_1), IC901.42 (DGND_2), IC901.49 (EP), IC902.4 (PG), IC902.6 (GND), IC902.11 (EP), J101.2, J101.3 (2), J101.4 (2), J101.5 (2), J701.1, J701.37, J701.38, J901.1, J901.37, J901.38, J902.2, J902.3 (2), J902.4 (2), J902.5 (2), R101.2, R204.2, R205.2, R615.1, R618.1, R619.1, R703.1, R704.1, R706.1, R708.1, R709.1, R711.1, R902.2, R903.1, R904.2, R906.1, R907.1, R909.1, T101.3 (S2), T101.4 (P2), T601.4 (P2), T901.4 (P2), T902.3 (S2), TVS101.1 (K), TVS901.1 (K), U902.3 (GND), X801.1 (NC/GND), X801.2 (NC/GND), X801.3 (GND)
I2C_SCL: IC801.16 (SCLK), J901.36, R801.1
I2C_SDA: IC801.18 (SDA/SDIO), J901.33, R802.1
LNA_N: C614.2, IC403.8 (RF_COM), R623.1
LNA_P: C613.2, IC402.8 (RF_COM), R622.1
MASTER_LPF_IN: IC201.19 (RF8), L348.1
MASTER_LPF_OUT: IC202.19 (RF8), L356.2
unnamed: C102.1, FB102.2, IC101.1 (IN), IC101.3 (EN)
unnamed: C201.2, C203.2, FB201.2, IC203.3 (VIN), IC203.8 (EN-), IC203.12 (EN+)
unnamed: C204.1, IC203.9 (C-)
unnamed: C204.2, IC203.10 (C+)
unnamed: C206.2, IC203.5 (CP)
unnamed: C301.1, C302.1, L304.1
unnamed: C303.1, C304.1, L305.1
unnamed: C310.1, C311.1, L309.1
unnamed: C312.1, C313.1, L310.1
unnamed: C314.1, L311.1
unnamed: C315.1, C316.1, L312.1
unnamed: C322.1, C323.1, L316.1
unnamed: C324.1, L317.1
unnamed: C325.1, C326.1, L318.1
unnamed: C327.1, L319.1
unnamed: C334.1, C335.1, L323.1
unnamed: C336.1, C337.1, L324.1
unnamed: C338.1, C339.1, L325.1
unnamed: C340.1, C341.1, L326.1
unnamed: C347.1, L330.1
unnamed: C348.1, C349.1, L331.1
unnamed: C350.1, L332.1
unnamed: C351.1, L333.1
unnamed: C355.1, L337.1
unnamed: C356.1, L338.1
unnamed: C357.1, L339.1
unnamed: C358.1, C359.1, L340.1
unnamed: C363.1, L344.1
unnamed: C364.1, L345.1
unnamed: C365.1, L346.1
unnamed: C366.1, L347.1
unnamed: C367.1, C368.1, L349.2
unnamed: C369.1, C370.1, L351.2
unnamed: C371.1, C372.1, L353.2
unnamed: C373.1, C374.1, L355.2
unnamed: C403.1, FB402.2, IC405.1 (IN), IC405.3 (EN)
unnamed: C501.1, FB501.2, IC501.1 (IN), IC501.3 (EN)
unnamed: C601.2, IC601.24 (+IN), R601.2
unnamed: C602.2, IC601.7 (-IN), R602.2
unnamed: C603.1, FB601.2, IC602.1 (IN_1), IC602.2 (IN_2), R614.2
unnamed: C604.1, IC602.7 (NR/SS), R616.2
unnamed: C605.2, IC601.5 (NFILT2)
unnamed: C606.2, IC601.6 (NFILT1)
unnamed: C607.1, IC601.19 (+FDBK)
unnamed: C608.1, IC601.12 (-FDBK)
unnamed: C617.2, R609.1, R610.2, R611.1, T602.2 (ST)
unnamed: C618.1, L605.1, R607.2, R609.2
unnamed: C618.2, L606.1, R608.2, R610.1
unnamed: C619.2, L607.2
unnamed: C625.2, L608.1
unnamed: C701.1, FB701.2, IC702.1 (IN_1), IC702.2 (IN_2), R702.2
unnamed: C706.1, IC702.7 (NR/SS), R704.2
unnamed: C709.1, FB702.2, IC703.1 (IN_1), IC703.2 (IN_2), R707.2
unnamed: C710.1, IC703.7 (NR/SS), R709.2
unnamed: C807.1, X801.4 (OUT)
unnamed: C807.2, IC801.8 (XA)
unnamed: C808.2, IC801.9 (XB)
unnamed: C904.1, IC901.13 (REFIO)
unnamed: C909.1, FB901.2, IC902.1 (IN_1), IC902.2 (IN_2), R905.2
unnamed: C910.1, IC902.7 (NR/SS), R907.2
unnamed: C919.1, T901.2 (ST)
unnamed: IC104.3 (~P/S), R102.2
unnamed: IC201.1 (LS), R201.1
unnamed: IC202.1 (LS), R202.1
unnamed: IC203.2 (FB+), R203.1, R204.1
unnamed: IC203.7 (FB-), R205.1, R206.1
unnamed: IC502.3 (~P/S), R501.2
unnamed: IC602.3 (EN_UV), R614.1, R615.2
unnamed: IC602.5 (FB_PG), R617.1, R618.2
unnamed: IC702.3 (EN_UV), R702.1, R703.2
unnamed: IC702.5 (FB_PG), R705.1, R706.2
unnamed: IC703.3 (EN_UV), R707.1, R708.2
unnamed: IC703.5 (FB_PG), R710.1, R711.2
unnamed: IC901.10 (PD), U902.4 (Y)
unnamed: IC901.14 (FSADJ), R901.1
unnamed: IC901.15 (DACREF), R901.2
unnamed: IC902.3 (EN_UV), R905.1, R906.2
unnamed: IC902.5 (FB_PG), R908.1, R909.2
unnamed: J901.3, R920.2
unnamed: J901.25, R912.2
unnamed: J901.26, R913.1
unnamed: J901.27, R910.2
unnamed: J901.28, R911.1
unnamed: J901.29, R918.2
unnamed: J901.30, R914.1
unnamed: J901.31, R917.2
unnamed: J901.32, R915.1
unnamed: J901.34, R916.1
unnamed: J901.35, R921.2
unnamed: L601.2, L611.1, R603.1, R620.2
unnamed: L602.1, L611.2, R604.2, R620.1
unnamed: L603.2, L612.1, R605.2, R621.1
unnamed: L604.1, L612.2, R606.1, R621.2
unnamed: L605.2, L607.1, L609.1
unnamed: L606.2, L608.2, L610.1
unnamed: L609.2, R612.1
unnamed: L610.2, R613.1
unnamed: R607.1, T602.3 (S2)
unnamed: R608.1, T602.1 (S1)
unnamed: R616.1, R619.2
RAND: IC701.63 (RAND), R920.1
RF_F1_S1: L301.2, L302.1, L304.2
RF_F1_S2: L302.2, L303.1, L305.2
RF_F2_S1: C306.2, C309.2, L306.1
RF_F2_S2: C305.1, C307.1, L306.2, L309.2, L310.2
RF_F2_S3: C305.2, C307.2, L307.1
RF_F2_S4: C308.1, L307.2, L311.2, L312.2
RF_F2_S5: C308.2, L308.1
RF_F3_S1: C318.2, L313.1
RF_F3_S2: C317.1, C319.1, L313.2, L316.2, L317.2
RF_F3_S3: C317.2, C319.2, L314.1
RF_F3_S4: C320.1, C321.1, L314.2, L318.2, L319.2
RF_F3_S5: C320.2, C321.2, L315.1
RF_F4_S1: C329.2, C332.2, L320.1
RF_F4_S2: C328.1, C330.1, L320.2, L323.2, L324.2
RF_F4_S3: C328.2, C330.2, L321.1
RF_F4_S4: C331.1, C333.1, L321.2, L325.2, L326.2
RF_F4_S5: C331.2, C333.2, L322.1
RF_F5_S1: C342.2, C345.2, L327.1
RF_F5_S2: C343.1, C346.1, L327.2, L330.2, L331.2
RF_F5_S3: C343.2, C346.2, L328.1
RF_F5_S4: C344.1, L328.2, L332.2, L333.2
RF_F5_S5: C344.2, L329.1
RF_F6_S1: C352.2, L334.1
RF_F6_S2: C353.1, L334.2, L337.2, L338.2
RF_F6_S3: C353.2, L335.1
RF_F6_S4: C354.1, L335.2, L339.2, L340.2
RF_F6_S5: C354.2, L336.1
RF_F7_S1: C360.2, L341.1
RF_F7_S2: C361.1, L341.2, L344.2, L345.2
RF_F7_S3: C361.2, L342.1
RF_F7_S4: C362.1, L342.2, L346.2, L347.2
RF_F7_S5: C362.2, L343.1
RF_FILTR_IN_1: IC201.24 (RF1), L301.1
RF_FILTR_IN_2: C306.1, C309.1, IC201.2 (RF2)
RF_FILTR_IN_3: C318.1, IC201.4 (RF3)
RF_FILTR_IN_4: C329.1, C332.1, IC201.6 (RF4)
RF_FILTR_IN_5: C342.1, C345.1, IC201.13 (RF5)
RF_FILTR_IN_6: C352.1, IC201.15 (RF6)
RF_FILTR_IN_7: C360.1, IC201.17 (RF7)
RF_FILTR_OUT_1: IC202.24 (RF1), L303.2
RF_FILTR_OUT_2: IC202.2 (RF2), L308.2
RF_FILTR_OUT_3: IC202.4 (RF3), L315.2
RF_FILTR_OUT_4: IC202.6 (RF4), L322.2
RF_FILTR_OUT_5: IC202.13 (RF5), L329.2
RF_FILTR_OUT_6: IC202.15 (RF6), L336.2
RF_FILTR_OUT_7: IC202.17 (RF7), L343.2
RF_M_S1: L348.2, L349.1, L350.1
RF_M_S2: L350.2, L351.1, L352.1
RF_M_S3: L352.2, L353.1, L354.1
RF_M_S4: L354.2, L355.1, L356.1
RF_TX_OUT: C913.2, J902.1
RF_TX_T1: C913.1, R902.1, T902.1 (S1), TVS901.2 (A)
RX_1: IC104.14 (RF2), IC401.3 (RF1)
RX_ATT_IN: C101.2, IC104.5 (RF1)
RX_IN_N: IC403.3 (RF1), T602.4 (P2)
RX_IN_P: IC402.3 (RF1), T602.6 (P1)
RX_LNA_IN_N: C602.1, R602.1, T601.1 (S1)
RX_LNA_IN_P: C601.1, R601.1, T601.3 (S2)
RX_LNA_OUT_N: C608.2, C614.1, IC601.13 (-OUT), L603.1, R605.1, R623.2
RX_LNA_OUT_P: C607.2, C613.1, IC601.18 (+OUT), L602.2, R604.1, R622.2
RX_T: J101.1, T101.6 (P1)
RX_TX_1: IC201.22 (RFC), IC401.8 (RF_COM)
RX_TX_2: IC202.22 (RFC), IC502.5 (RF1)
RX_TX_3: IC502.14 (RF2), T601.6 (P1)
RX_TX_MODE: IC401.16 (CTL2), IC402.16 (CTL2), IC403.16 (CTL2), IC701.19 (SHDN), R916.2, U902.2 (A)
RX_T_OUT: C101.1, R101.1, T101.1 (S1), TVS101.2 (A)
TX_1: IC401.13 (RF2), T901.6 (P1)
TX_D0: IC901.2 (B0), J901.20
TX_D1: IC901.1 (B1), J901.19
TX_D2: IC901.48 (B2), J901.18
TX_D3: IC901.47 (B3), J901.17
TX_D4: IC901.46 (B4), J901.16
TX_D5: IC901.45 (B5), J901.15
TX_D6: IC901.44 (B6), J901.14
TX_D7: IC901.41 (B7), J901.13
TX_D8: IC901.40 (B8), J901.12
TX_D9: IC901.39 (B9), J901.11
TX_D10: IC901.38 (B10), J901.10
TX_D11: IC901.37 (B11), J901.9
TX_D12: IC901.36 (B12), J901.8
TX_D13: IC901.35 (B13), J901.7
TX_D14: IC901.34 (B14), J901.6
TX_D15: IC901.33 (B15), J901.5
TX_OUT_N: IC403.13 (RF2), T902.4 (P2)
TX_OUT_P: IC402.13 (RF2), T902.6 (P1)
TX_SEL0: IC901.30 (SEL0), J901.4
TX_XOR: IC901.3 (XOR), J901.21

Notes on the sheet:
(RX pass to ADC)
BPF-60MHz Eliptic 47-73 MHz band
Design: Block 6 - Differential Output with 15.9dB Gain. v1.0 Function: Converts single-ended signal to differential signal for driving LTC2209 16-bit ADC.
Block 8: Clock Generator v.1.0
BPF-6MHz Eliptic 4-8 Mhz band
(from Block 6)
Clean-up Filter диференціальний фільтр низьких частот
RF-OUT
BPF-11.8MHz Eliptic 8-15.5 Mhz band
(from Block 4 LNA & bypass)
Block 7: LTC2209 16 bit ADC Integration Design (CMOS Mode) v.1.0 130 MSPS ADC directly on the main RF frontend PCB
(to Block 7)
Design: Block 4 - RX/TX Switch v1.0
(from Block 9)
BPF-40MHz Eliptic 30-50 Mhz band
(to Block 2)
(TX pass to OUT) Block 9
DEsign: Block 1 SDR RF Frontend v1.0 provides the complete RF front-end signal path from antenna connector through DSA 1 to preselector input
(from Block 4 RX/TX Switch)
диференціальний конденсатор
DEsign: Block 2 Filter Switch v1.0
Low-Pass Elliptic Dual Passband Gain = 0 dB Passband Ripple (R) = 0.10103 dB Passband Frequency (Fc) = 7.2e+007Hz Stopband Attenuation (A) = 40 dB Stopband Frequency (Fs) = 7.5e+007 Hz Impedance Scale Factor=1
(to Block 4 - LNA)
(to Block 4 - RX/TX Switch)
BPF-2.8MHz Eliptic 1.5-4 Mhz band
BPF-22.5MHz Eliptic 15-30 Mhz band
Block 9: MAX5885 DAC
DEsign: Block 5 Attenuator DSA2
(from Block 1)
DEsign: Block 3 Filter BANK
LPF-1.6MHz Eliptic 0-1.6 Mhz band
RF-IN
(from Block 5 - DSA2)
(from Block 1 - Frontend)
